themarcman314/bouton_a_un_moment_donne/data/foyer.jpg

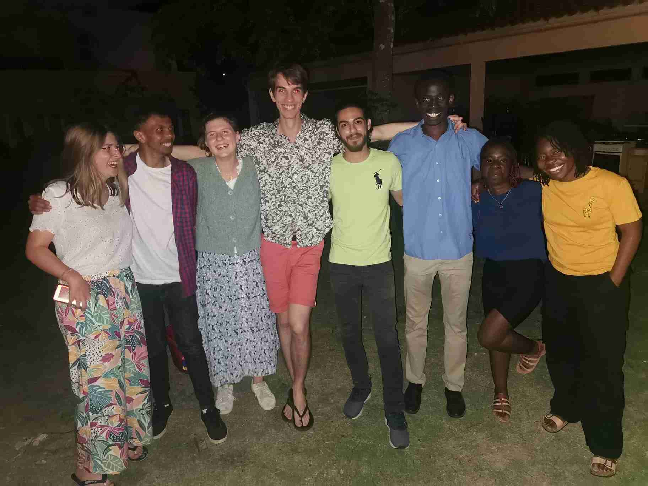
data/foyer.jpg
